nazililham11/measurement_tool/Assets/skema_v2.png

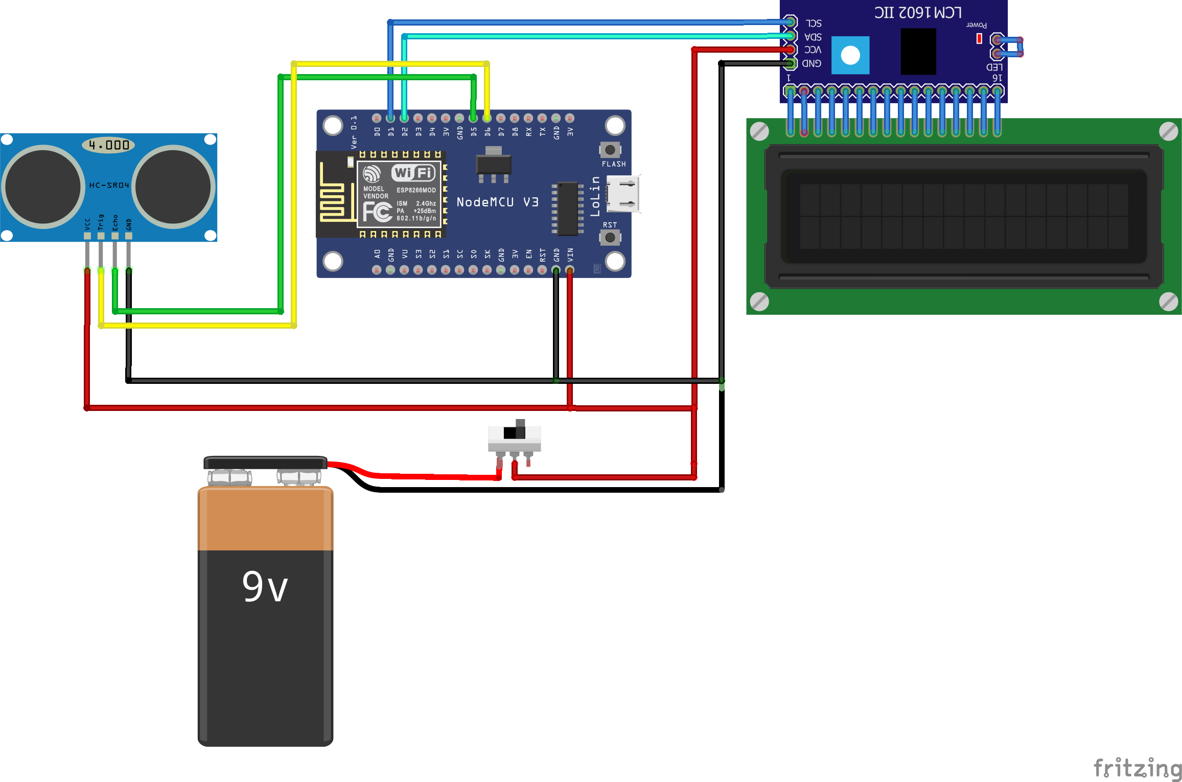
Assets/skema_v2.png
